bobby1321/High-Current-5V-Regulator/LTSpice/4S Battery Meter.asc

C1: cap; 0.1µF
D1: zener; BZX84C6V2L
D2: LED
D3: LED
D4: LED
D5: LED
D6: LED
D7: diode; 1N4148
R1: res; 120
R2: res; 6.8k
R3: res; 820
R4: res; 820
R5: res; 820
R6: res; 6.8k
R7: res; 8.2k
R8: res; {R_LED}
R9: res; {R_LED}
R10: res; {R_LED}
R11: res; {R_LED}
R12: res; {R_LED}
R13: res; 6.8k
R14: res; {R_TRIM}
U5: LM339
U6: LM339
U7: LM339
U8: LM339
V1: battery; 12.5
Named nets: 0
;tran 0 1 0
.dc V1 5 9
.param R_LED=5.1k R_TRIM=1k
For 2S - R1 = 120, R2 = 6.8K, R13 = 6.8K, R7 = 8.2K, R6 = 6.8K
For 4S - R1 = 1K, R2 = 6.8K, R13 = 8.2K, R7 = 15K, R6 = 5.1K
